takayoshiotake/octave-12-key-macropad/study/key-matrix/key-matrix.kicad_sch

## KiCad design study/key-matrix/key-matrix.kicad_sch (2022-02-23)

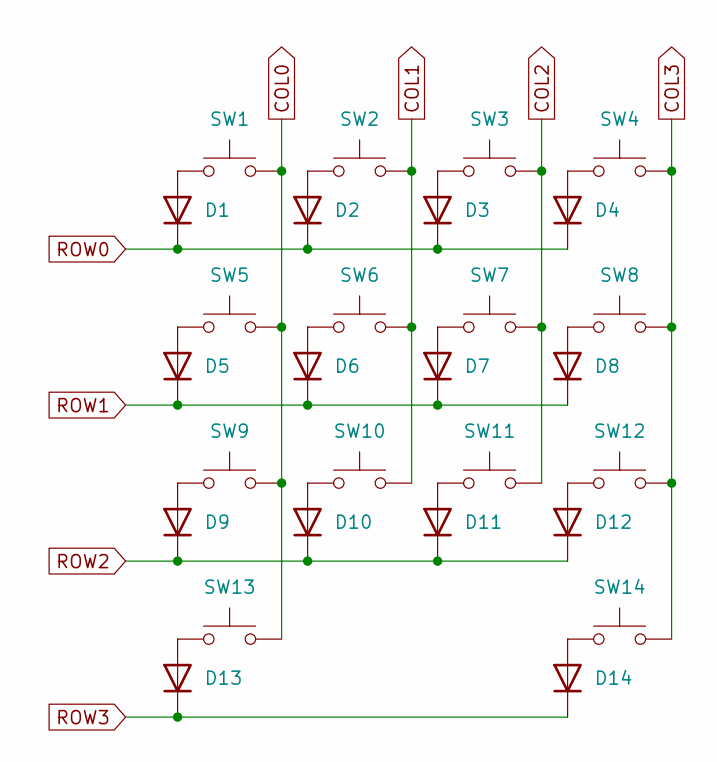
[picture p30: schematic key-matrix.kicad_sch]

Parts:
D1, D2, D3, D4, D5, D6, D7, D8, D9, D10, D11, D12, D13, D14: D
SW1, SW2, SW3, SW4, SW5, SW6, SW7, SW8, SW9, SW10, SW11, SW12, SW13, SW14: SW_Push

Connections:
COL0: SW1.2, SW5.2, SW9.2, SW13.2
COL1: SW2.2, SW6.2, SW10.2
COL2: SW3.2, SW7.2, SW11.2
COL3: SW4.2, SW8.2, SW12.2, SW14.2
unnamed: D1.2 (A), SW1.1
unnamed: D2.2 (A), SW2.1
unnamed: D3.2 (A), SW3.1
unnamed: D4.2 (A), SW4.1
unnamed: D5.2 (A), SW5.1
unnamed: D6.2 (A), SW6.1
unnamed: D7.2 (A), SW7.1
unnamed: D8.2 (A), SW8.1
unnamed: D9.2 (A), SW9.1
unnamed: D10.2 (A), SW10.1
unnamed: D11.2 (A), SW11.1
unnamed: D12.2 (A), SW12.1
unnamed: D13.2 (A), SW13.1
unnamed: D14.2 (A), SW14.1
ROW0: D1.1 (K), D2.1 (K), D3.1 (K), D4.1 (K)
ROW1: D5.1 (K), D6.1 (K), D7.1 (K), D8.1 (K)
ROW2: D9.1 (K), D10.1 (K), D11.1 (K), D12.1 (K)
ROW3: D13.1 (K), D14.1 (K)
